LigasN/NormalMapScanner/3D_modeling/stand_model/normalmap.bmp

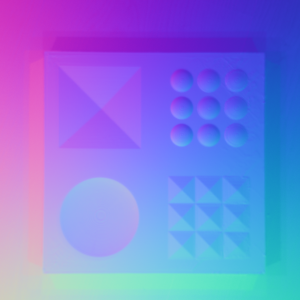
3D_modeling/stand_model/normalmap.bmp
