LigasN/NormalMapScanner/3D_modeling/stand_model/normalMapCandidate.png

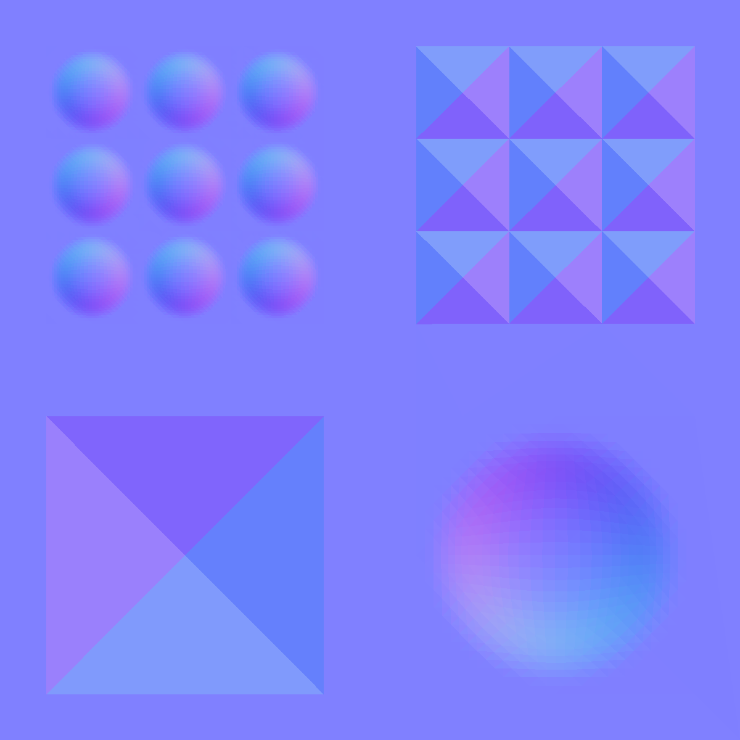
3D_modeling/stand_model/normalMapCandidate.png
