LigasN/NormalMapScanner/docs/assets/pinout/NULCEO-F446RE_pinout.jpg

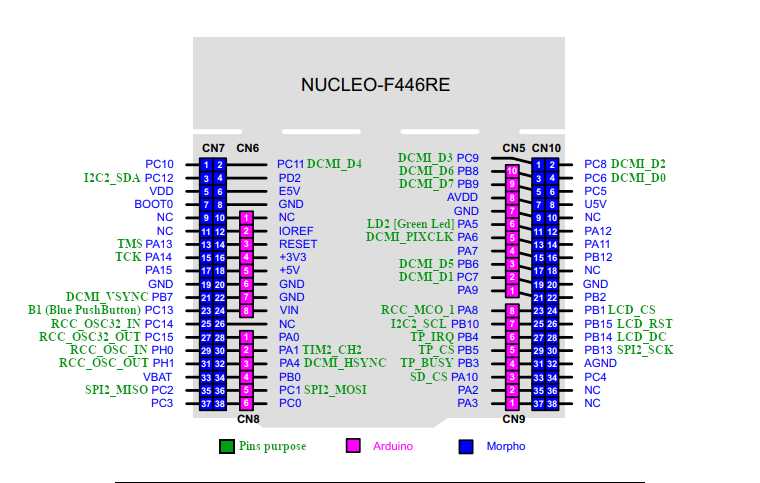
docs/assets/pinout/NULCEO-F446RE_pinout.jpg
