LigasN/NormalMapScanner/py_src/assets/preview.jpg

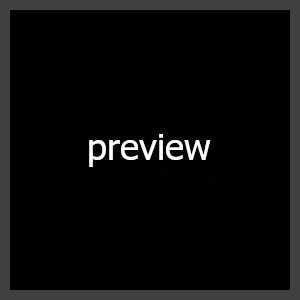
py_src/assets/preview.jpg
