LigasN/NormalMapScanner/3D_modeling/construction/images/parts/bar_285mm_annotations.jpg

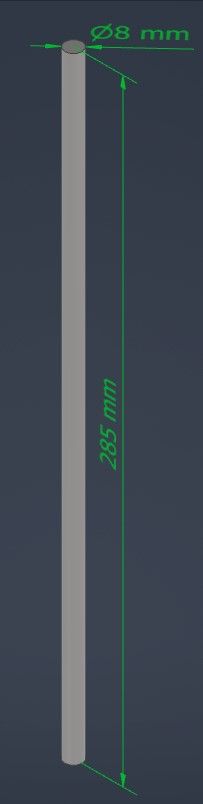
3D_modeling/construction/images/parts/bar_285mm_annotations.jpg
