LigasN/NormalMapScanner/3D_modeling/construction/images/parts/bar_connector_left_annotations.jpg

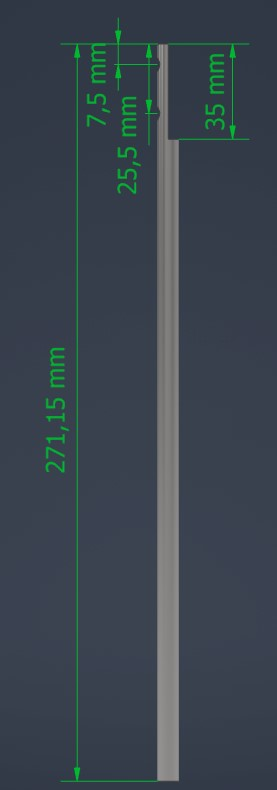
3D_modeling/construction/images/parts/bar_connector_left_annotations.jpg
