LigasN/NormalMapScanner/3D_modeling/construction/images/parts/barrel_hinge_left_annotations.jpg

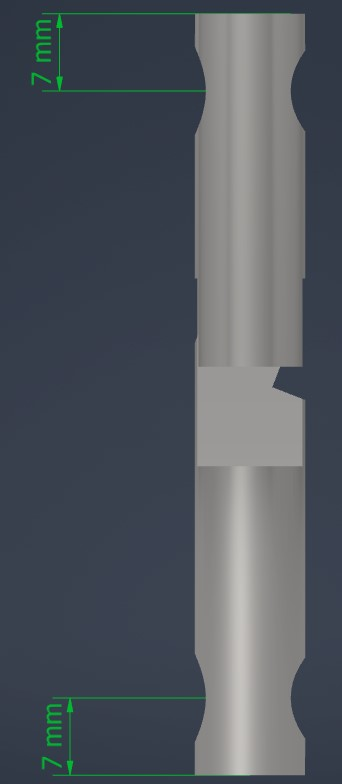
3D_modeling/construction/images/parts/barrel_hinge_left_annotations.jpg
