LigasN/NormalMapScanner/3D_modeling/construction/images/parts/barrel_hinge_top_annotations.jpg

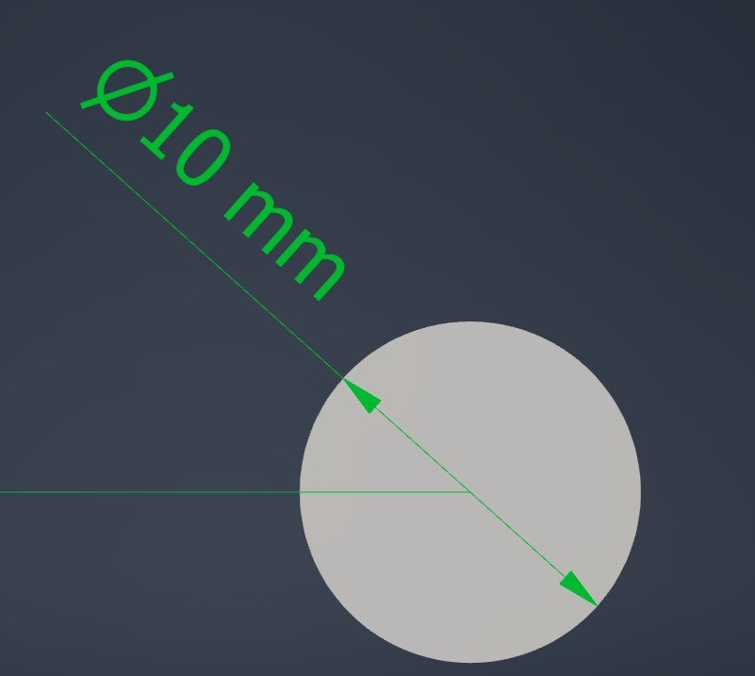
3D_modeling/construction/images/parts/barrel_hinge_top_annotations.jpg
