LigasN/NormalMapScanner/3D_modeling/construction/images/parts/camera_box.jpg

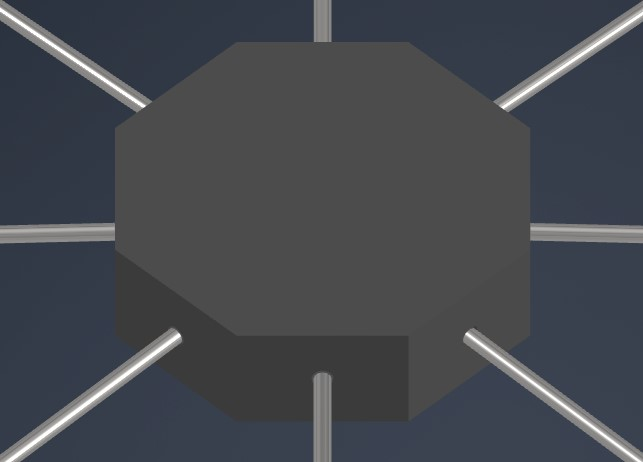
3D_modeling/construction/images/parts/camera_box.jpg
