LigasN/NormalMapScanner/3D_modeling/construction/images/parts/flat_bar.jpg

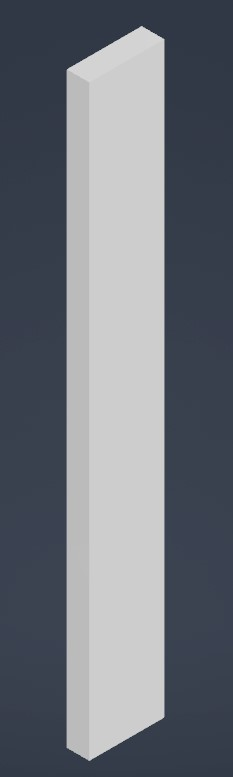
3D_modeling/construction/images/parts/flat_bar.jpg
