LigasN/NormalMapScanner/3D_modeling/construction/images/parts/flat_bar_annotations.jpg

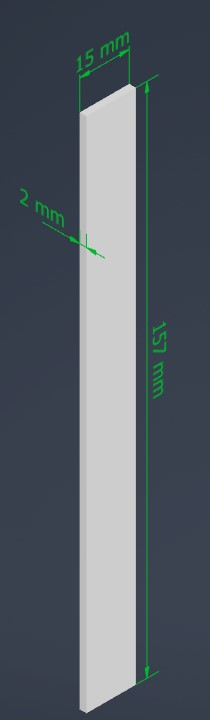
3D_modeling/construction/images/parts/flat_bar_annotations.jpg
