LigasN/NormalMapScanner/3D_modeling/construction/images/parts/pipe_300mm_annotations.jpg

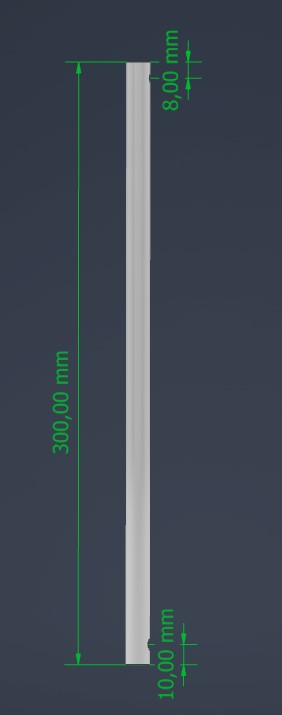
3D_modeling/construction/images/parts/pipe_300mm_annotations.jpg
