LigasN/NormalMapScanner/3D_modeling/construction/images/parts/pipe_connector.jpg

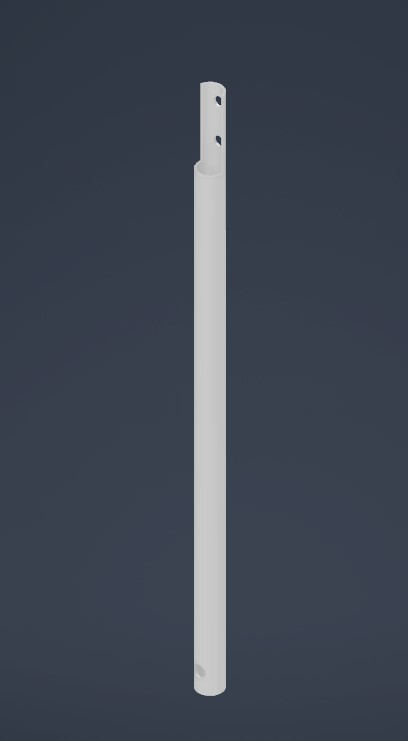
3D_modeling/construction/images/parts/pipe_connector.jpg
