LigasN/NormalMapScanner/3D_modeling/construction/images/parts/pipe_connector_front_annotations.jpg

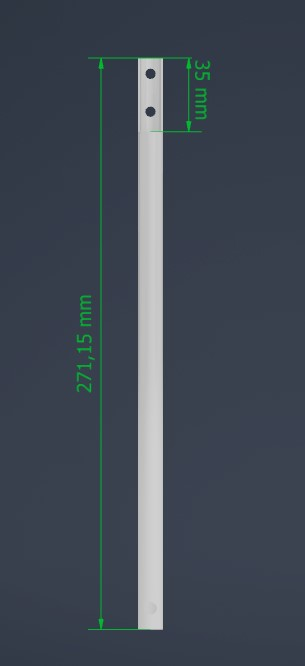
3D_modeling/construction/images/parts/pipe_connector_front_annotations.jpg
