LigasN/NormalMapScanner/3D_modeling/construction/images/parts/pipe_connector_left_annotations.jpg

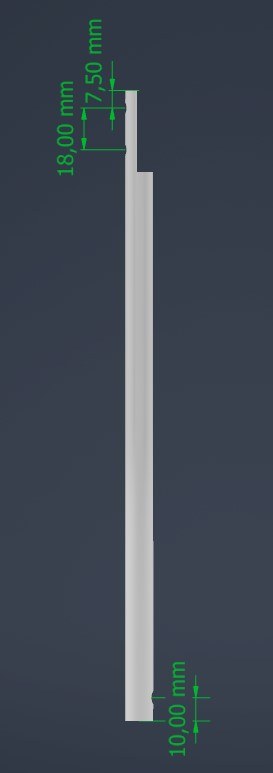
3D_modeling/construction/images/parts/pipe_connector_left_annotations.jpg
