LigasN/NormalMapScanner/3D_modeling/construction/images/assemblies/arm.jpg

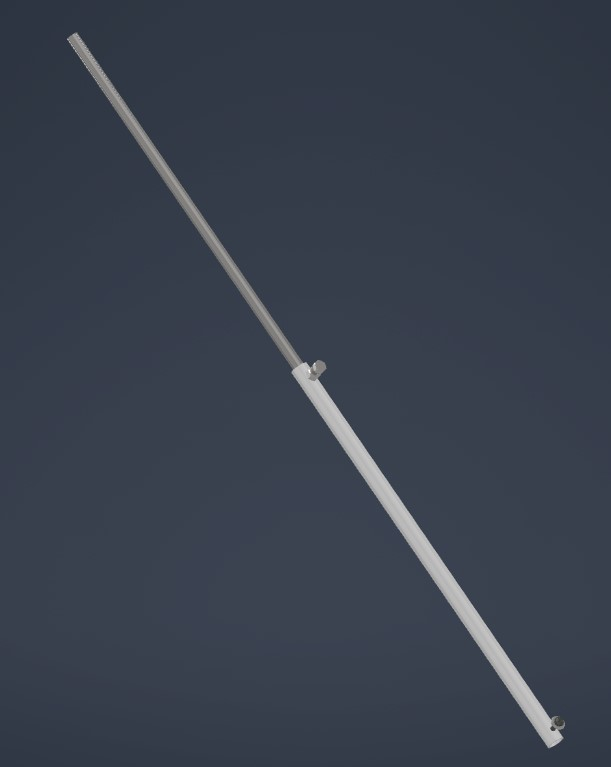
3D_modeling/construction/images/assemblies/arm.jpg
