LigasN/NormalMapScanner/3D_modeling/construction/images/assemblies/arm_annotations.jpg

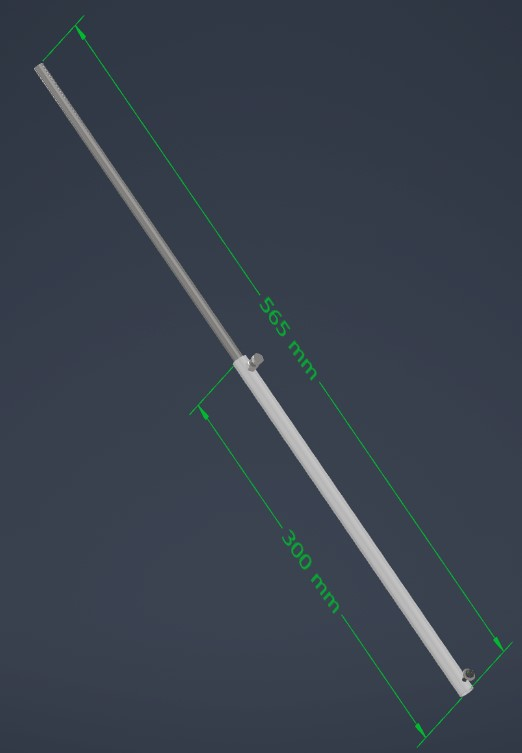
3D_modeling/construction/images/assemblies/arm_annotations.jpg
