LigasN/NormalMapScanner/3D_modeling/construction/images/assemblies/double_connector.jpg

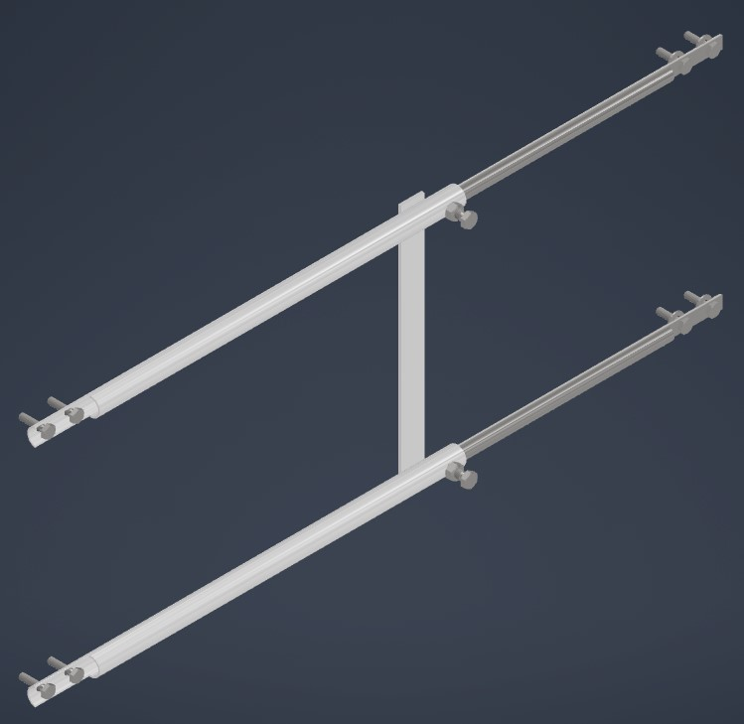
3D_modeling/construction/images/assemblies/double_connector.jpg
