LigasN/NormalMapScanner/3D_modeling/construction/images/assemblies/double_connector_max_annotations.jpg

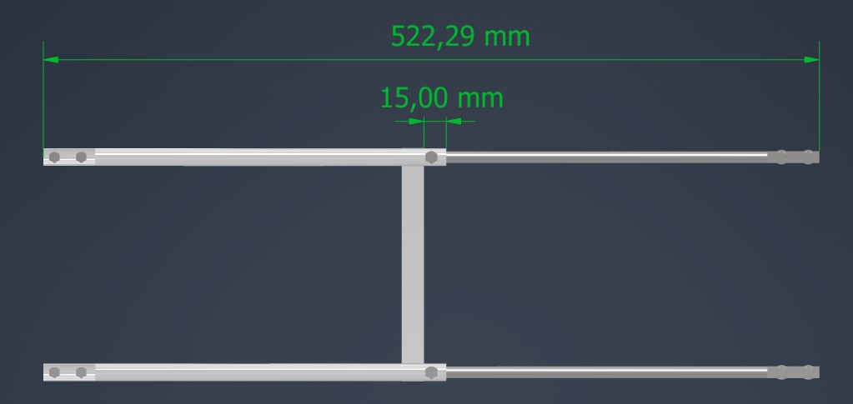
3D_modeling/construction/images/assemblies/double_connector_max_annotations.jpg
