LigasN/NormalMapScanner/3D_modeling/construction/images/assemblies/leg.jpg

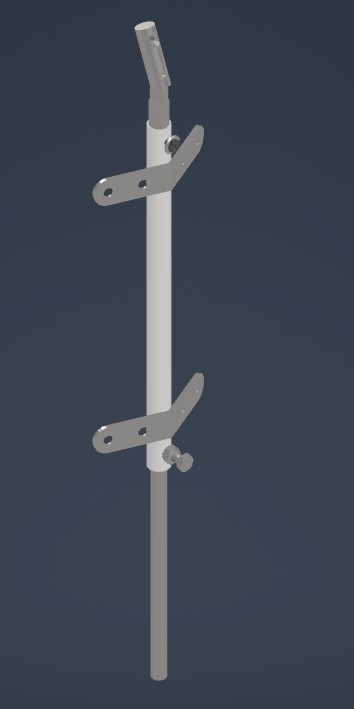
3D_modeling/construction/images/assemblies/leg.jpg
