LigasN/NormalMapScanner/3D_modeling/construction/images/assemblies/leg_annotations.jpg

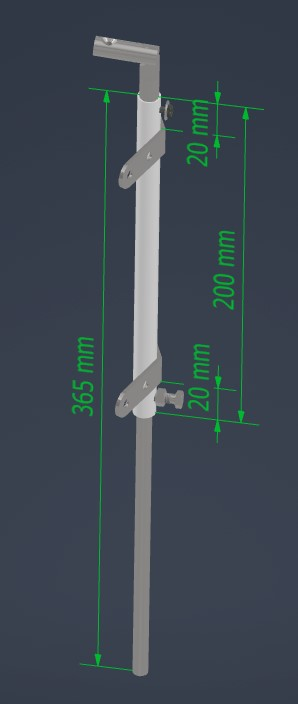
3D_modeling/construction/images/assemblies/leg_annotations.jpg
