LigasN/NormalMapScanner/3D_modeling/construction/images/assemblies/stand.jpg

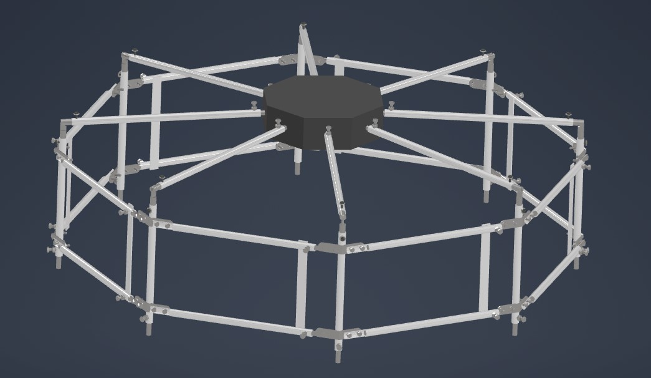
3D_modeling/construction/images/assemblies/stand.jpg
