LigasN/NormalMapScanner/3D_modeling/construction/images/assemblies/stand_max.jpg

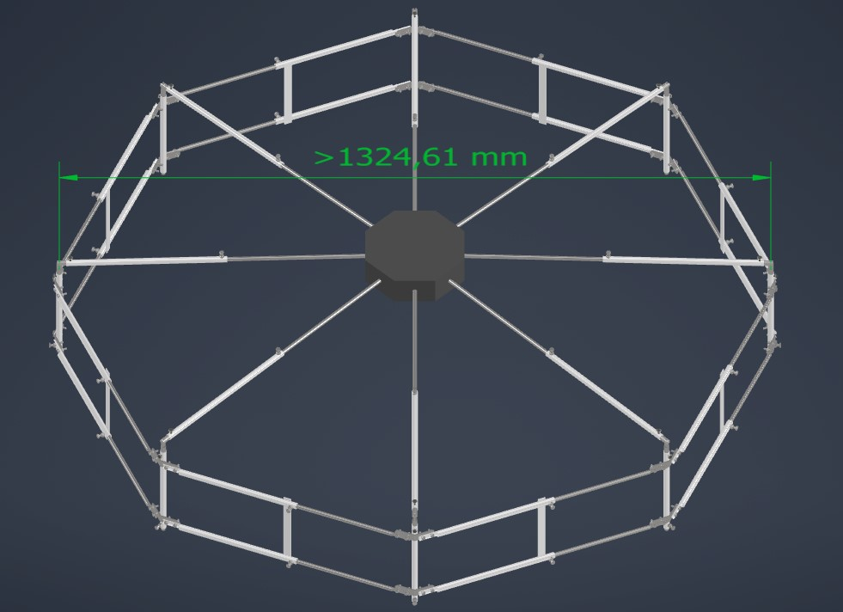
3D_modeling/construction/images/assemblies/stand_max.jpg
