LigasN/NormalMapScanner/3D_modeling/construction/images/assemblies/stand_min.jpg

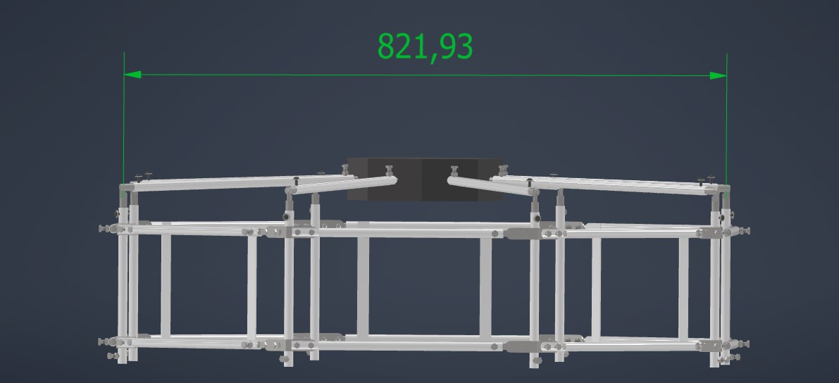
3D_modeling/construction/images/assemblies/stand_min.jpg
