LigasN/NormalMapScanner/docs/assets/stand_top_view/stand_top_view_measurements.jpg

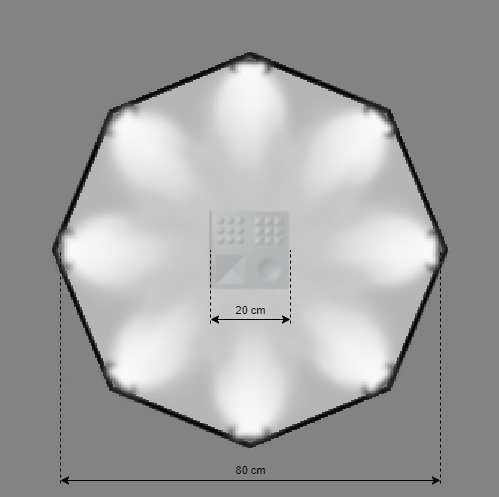
docs/assets/stand_top_view/stand_top_view_measurements.jpg
