LigasN/NormalMapScanner/py_src/normal_map/test_input/5.photos_2200x2200px/input_135.jpg

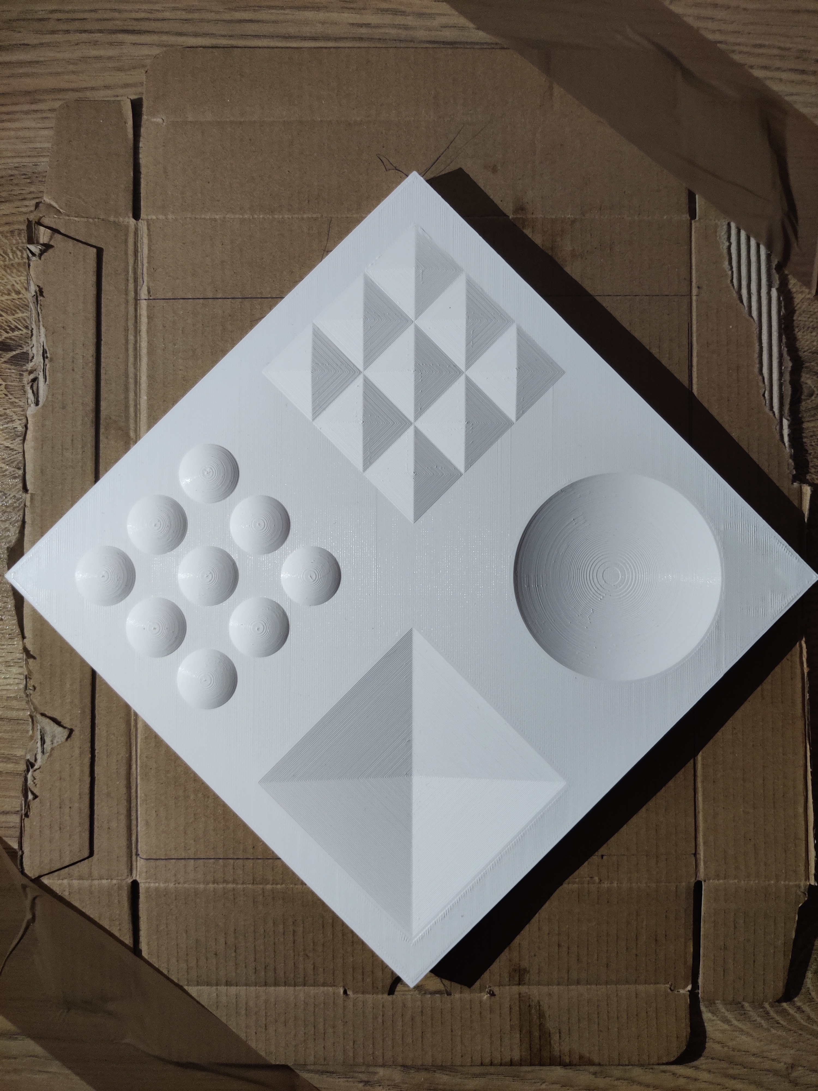
py_src/normal_map/test_input/5.photos_2200x2200px/input_135.jpg
