LigasN/NormalMapScanner/pcb/SwitchingTransistor.asc

Q3: npn; BCW66G
R4: res; 4.3k
R5: res; 75
R6: res; 75
R7: res; 22k
V1: voltage; 12
V2: voltage; PULSE(0 3.3 0 1u 1u 0.5 1)
Named nets: 0, VCC, GPIO
.tran 1
https://www.electricalelibrary.com/en/2018/07/02/how-to-polarize-the-bjt-transistor-part-1/
